mhamilt/harpsichord-jack-tracking/img/7-jack-pcb.png

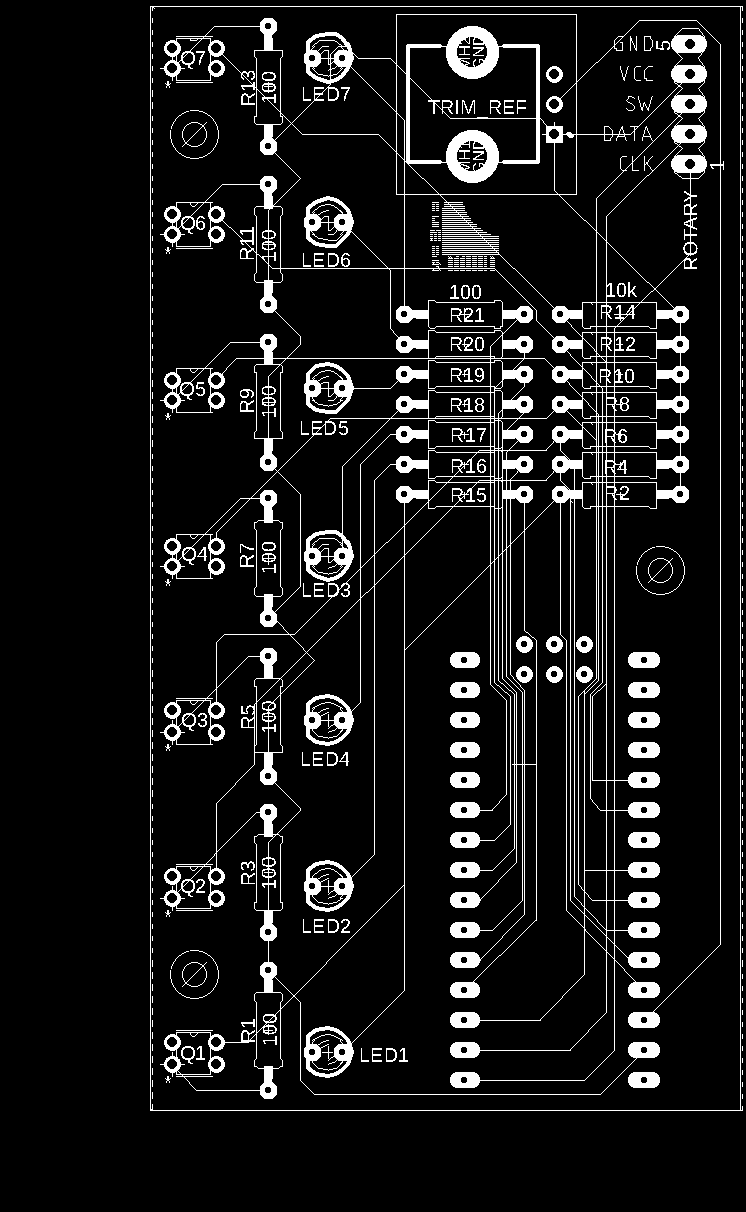
img/7-jack-pcb.png
