mhamilt/harpsichord-jack-tracking/img/49-key-bottom.jpeg

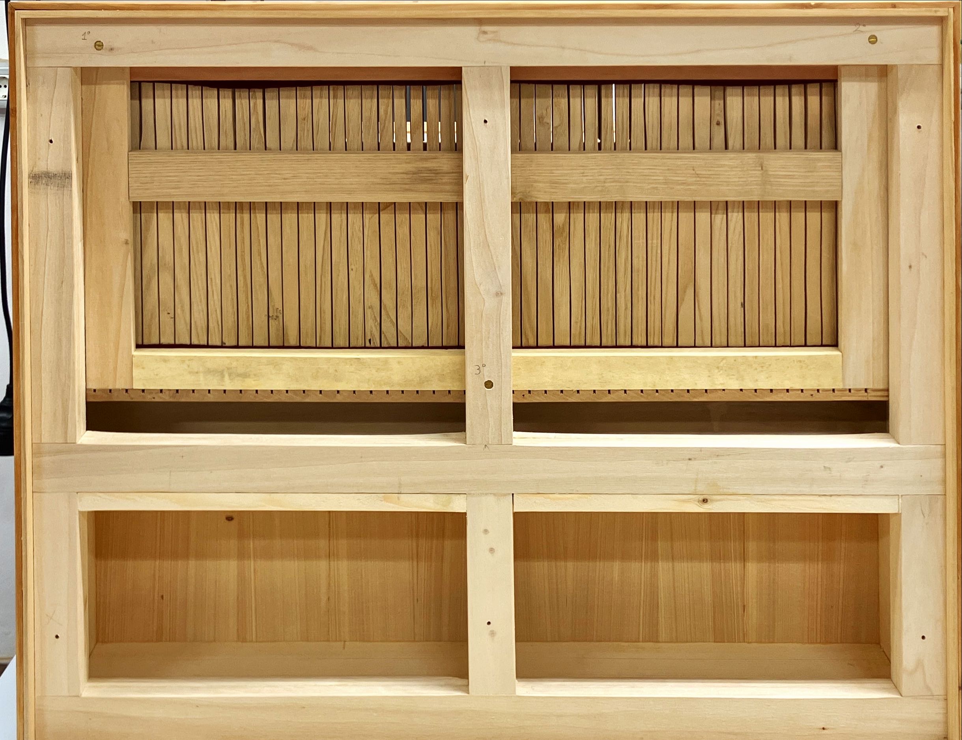
img/49-key-bottom.jpeg
