mhamilt/harpsichord-jack-tracking/img/49-key-jacks.jpeg

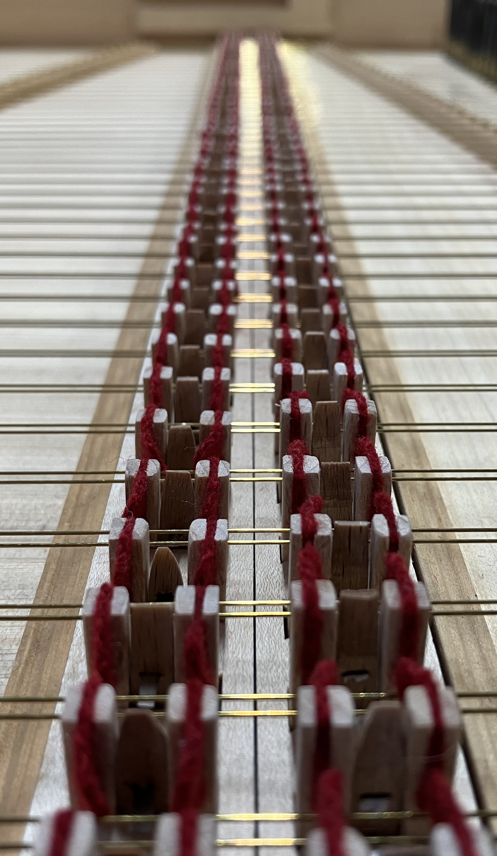
img/49-key-jacks.jpeg
