mhamilt/harpsichord-jack-tracking/img/IMG_1575.jpeg

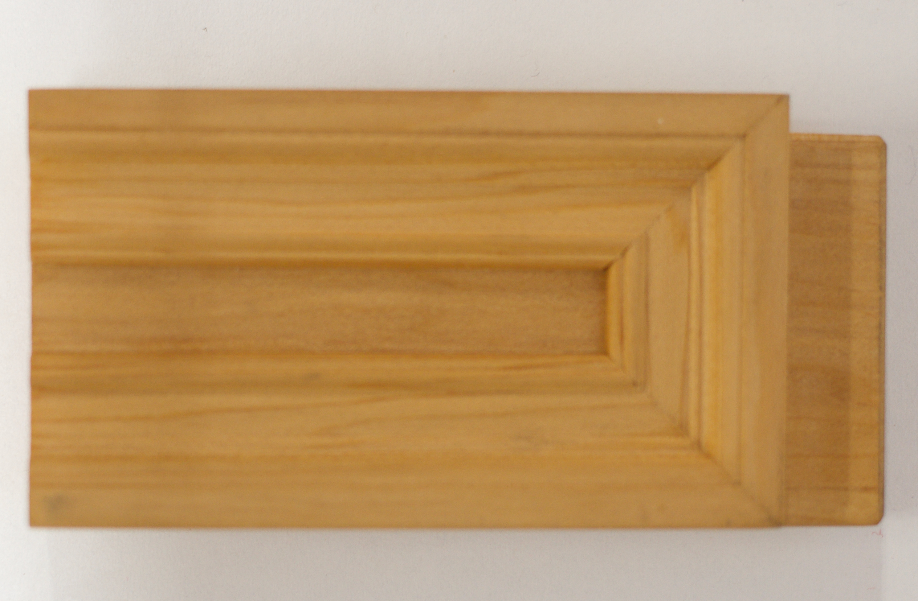
img/IMG_1575.jpeg
