mhamilt/harpsichord-jack-tracking/img/IMG_1578.jpeg

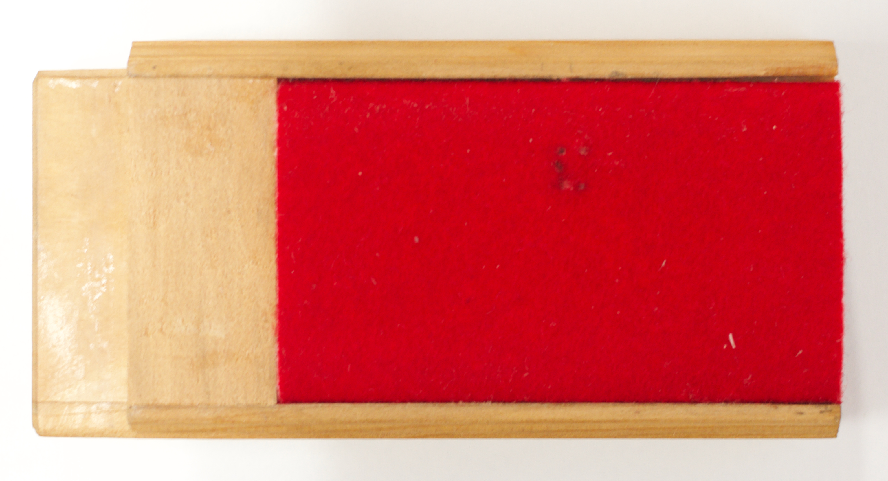
img/IMG_1578.jpeg
