mhamilt/harpsichord-jack-tracking/img/jacks.jpg

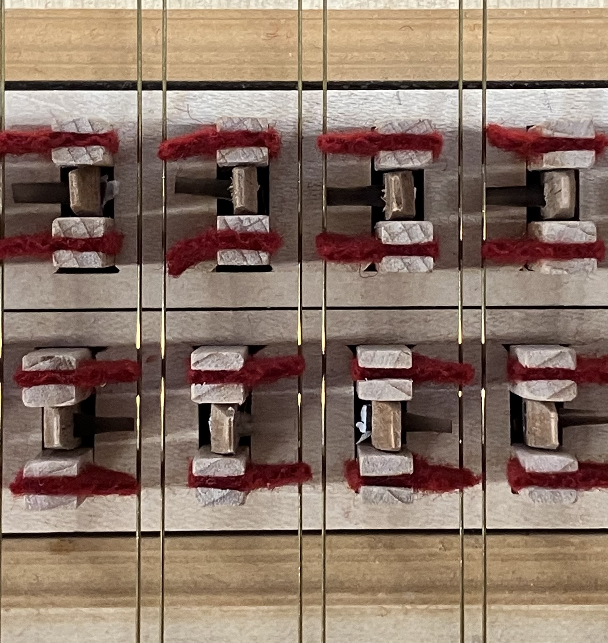
img/jacks.jpg
