mhamilt/harpsichord-jack-tracking/src/HapticHarpsichord/print_functions.ino

// void printJackStates() {
//   bool anyPrint = false;

//   if (jackStates[0] == PLUCK and prevStates[0] == RELEASED) {
//     Serial.print("Jack 1 Plucked ");
//     anyPrint = true;
//   }
//   if (jackStates[1] == PLUCK and prevStates[1] == RELEASED) {
//     Serial.print("Jack 2 Plucked ");
//     anyPrint = true;
//   }
//   if (jackStates[2] == PLUCK and prevStates[2] == RELEASED) {
//     Serial.print("Jack 3 Plucked ");
//     anyPrint = true;
//   }
//   if (anyPrint)
//     Serial.println();
// }

//-----------------------------------------------------------------------------

void printJackReading(byte index) {
  Serial.print("m:");
  Serial.print(0);
  Serial.print(' ');

  Serial.print("M:");
  Serial.print(1024);
  Serial.print(' ');
  
  Serial.print("kM:");
  Serial.print(sensorAvgMaxima[index]);
  Serial.print(' ');

  Serial.print("km:");
  Serial.print(sensorAvgMinima[index]);
  Serial.print(' ');

  Serial.print("K");
  Serial.print(index2key(index));
  Serial.print(":");
  Serial.print(readSensor(index));
  Serial.print(' ');
}

void printJackThreshold(byte index)
{
  Serial.print("T");
  Serial.print(index2key(index));
  Serial.print(":");
  Serial.print(pluckThresholds[index]);
}
