mhamilt/harpsichord-jack-tracking/src/QRE1113_Keyboard_7_note/debug_functions.ino

//-----------------------------------------------------------------------------
// Debug functions

void setupDebugMode() {
  Serial.println("DEBUG MODE");
  executeDebugMode = true;
  r.setChangedHandler(rotate);
  b.setDoubleClickHandler(doubleclick);
  b.setClickHandler(click);

  for (auto pin : ledPins) {    
    digitalWrite(pin, LOW);
  }
  digitalWrite(ledPins[r.getPosition()], HIGH);
}

void debugModeLoop() {
  r.loop();
  b.loop();
  updateSensorReadings();
  printCurrentKeyAndThresh();
}


void exitDebug() {
  writePluckToEEPROM();

  for (auto pin : ledPins) {
    pinMode(pin, OUTPUT);
    digitalWrite(pin, LOW);
  }
}
